rumankazi/project_morphius/Phase_2/arduino/evo_app_testing/serial_hm10/serial_hm10.ino

#include <SoftwareSerial.h>
#define LED_PIN 13

SoftwareSerial mySerial(8, 9); // RX, TX  
// Connect HM10      Arduino Uno
//     Pin 1/TXD          Pin 7
//     Pin 2/RXD          Pin 8

void setup() {  
  Serial.begin(9600);
  // If the baudrate of the HM-10 module has been updated,
  // you may need to change 9600 by another value
  // Once you have found the correct baudrate,
  // you can update it using AT+BAUDx command 
  // e.g. AT+BAUD0 for 9600 bauds
  mySerial.begin(9600);
}

void loop() {  
  int c;
  
  if (mySerial.available()) {
    c = mySerial.read();  
    Serial.println("Got input:");
    if (c != 0)
    {
      // Non-zero input means "turn on LED".
      Serial.println("  on");
      digitalWrite(LED_PIN, HIGH);
    }
    else
    {
      // Input value zero means "turn off LED".
      Serial.println("  off");
      digitalWrite(LED_PIN, LOW);
    }  
  }
}
