rumankazi/project_morphius/Phase_2/arduino/servo_testing/arduino-example-servomotor-360-1.0.0/sketchbook/servomotor-360/servomotor-360.ino

/*
 * Servomotor 360 degree
 *
 * Sample code to control a servo motor 360 degrees.
 */

#include <Servo.h>

int pin = 8;
int stop_position = 95;
int velocity = 20;

Servo servo;

void setup() {
  servo.attach(pin);
}

void loop() {
  servo.write(stop_position - velocity);
  delay(500);
  servo.write(stop_position + velocity);
  delay(500);
}
